BLEduino/bleduino-hardware/BLEduino/PDFs/BLEduino_PCB_copper_2.pdf

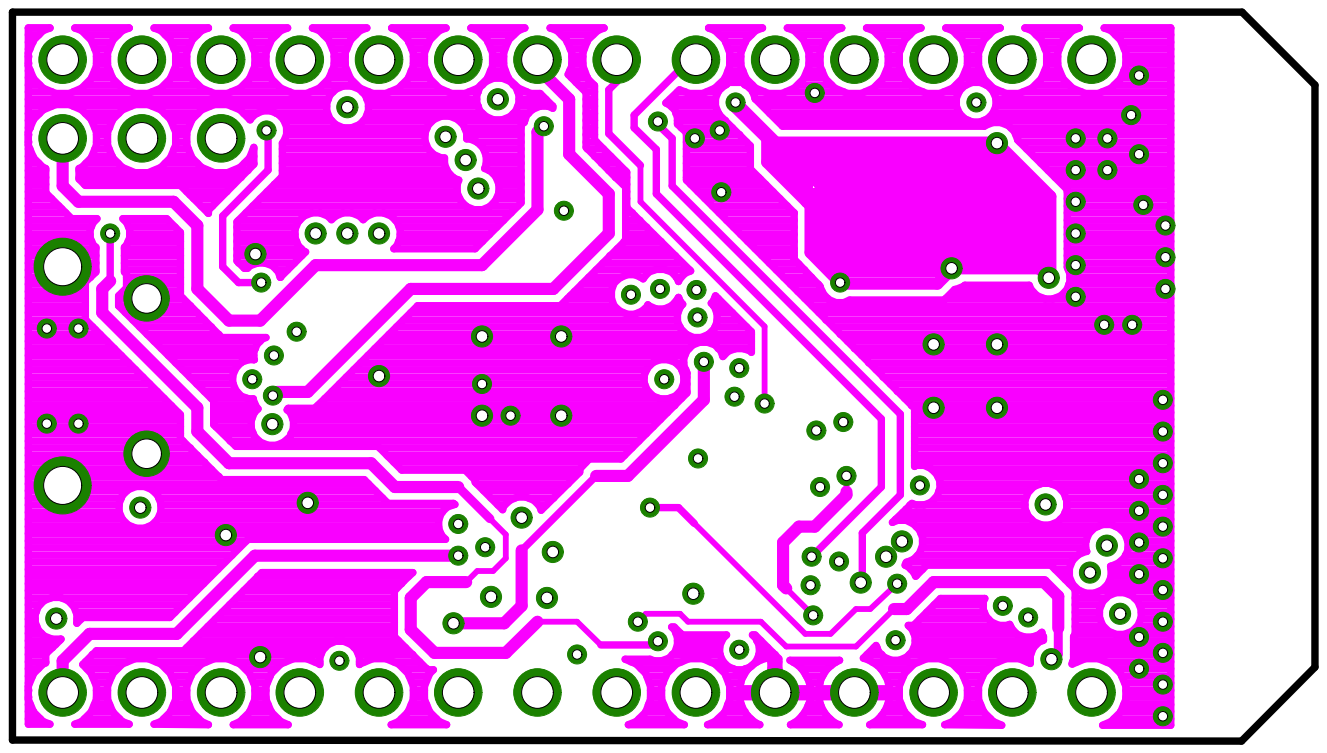
[picture p11: page 1]
