BLEduino/bleduino-hardware/BLEduino/PDFs/BLEduino_PCB_copper_3.pdf

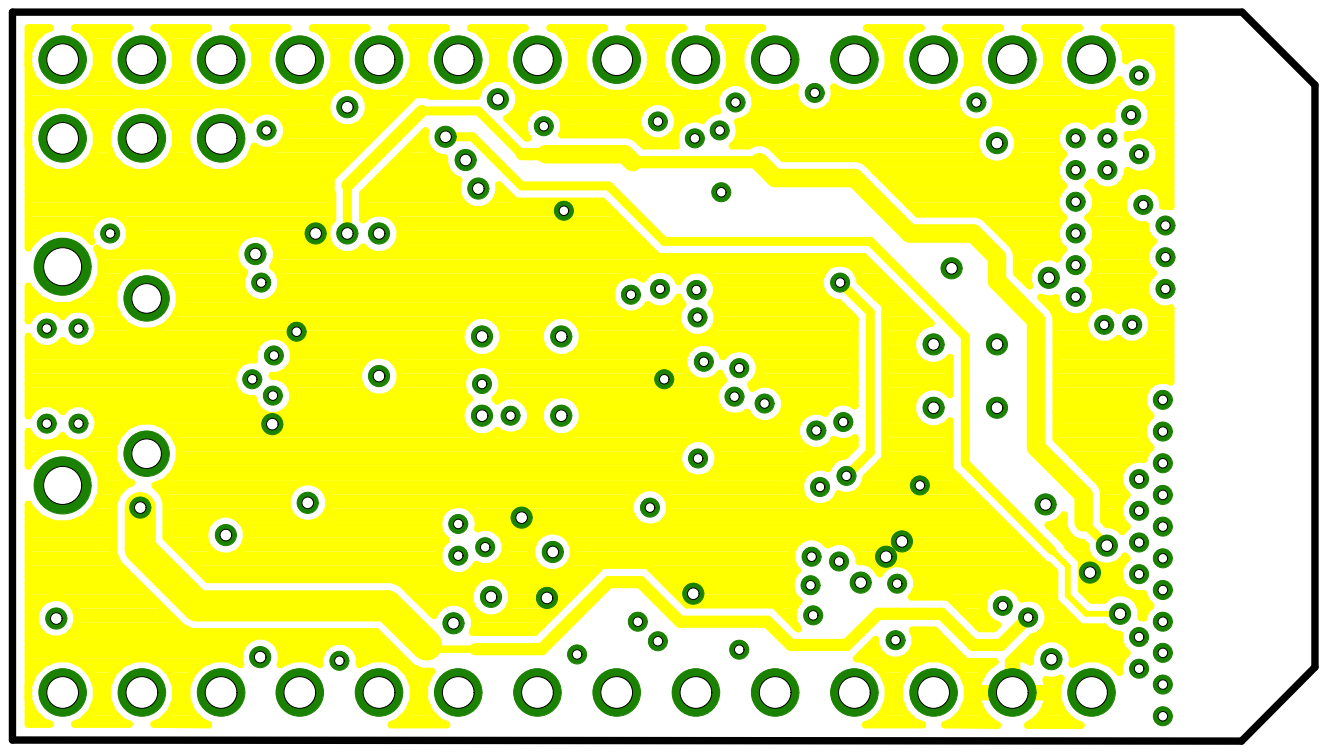
[picture p12: page 1]
