BLEduino/bleduino-hardware/BLEduino/PDFs/BLEduino_PCB_copper_4.pdf

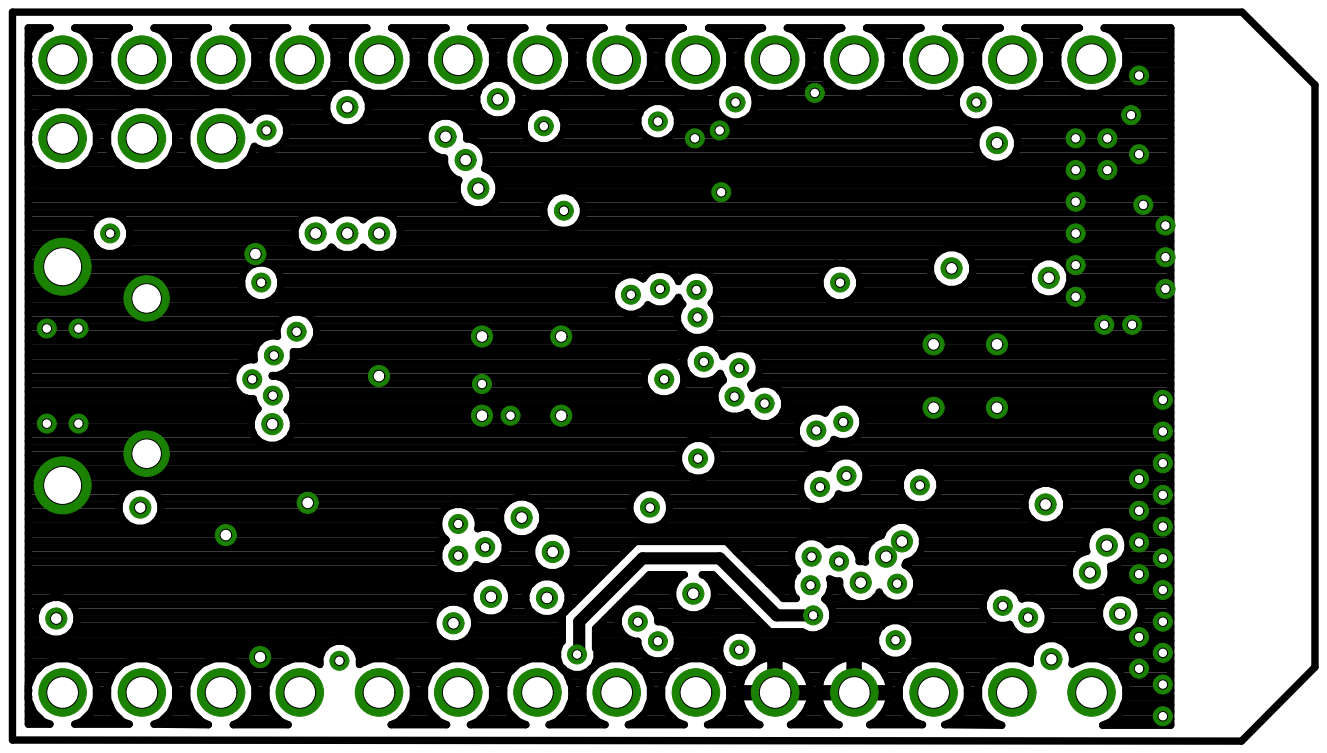
[picture p13: page 1]
