BLEduino/bleduino-hardware/BLEduino/PDFs/BLEduino_PCB_copper_5.pdf

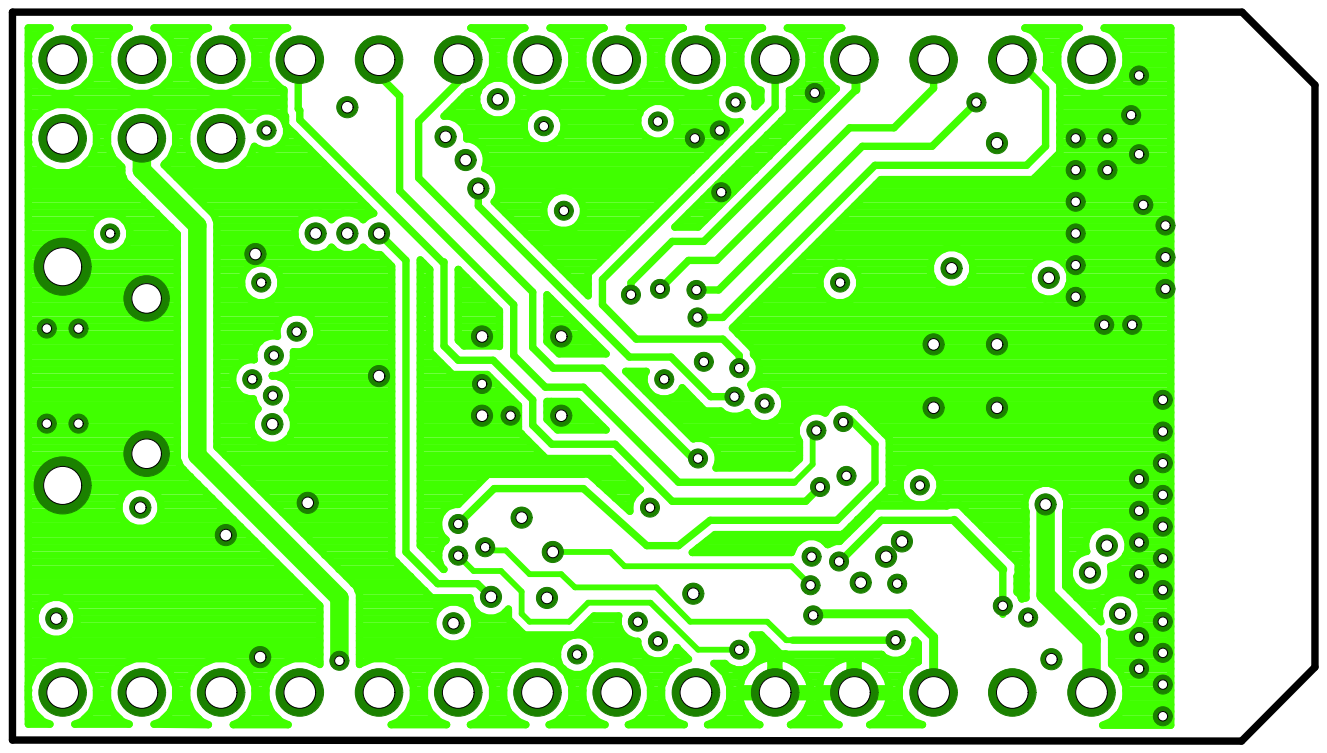
[picture p14: page 1]
