BLEduino/bleduino-hardware/BLEduino/PDFs/BLEduino_PCB_copper_6.pdf

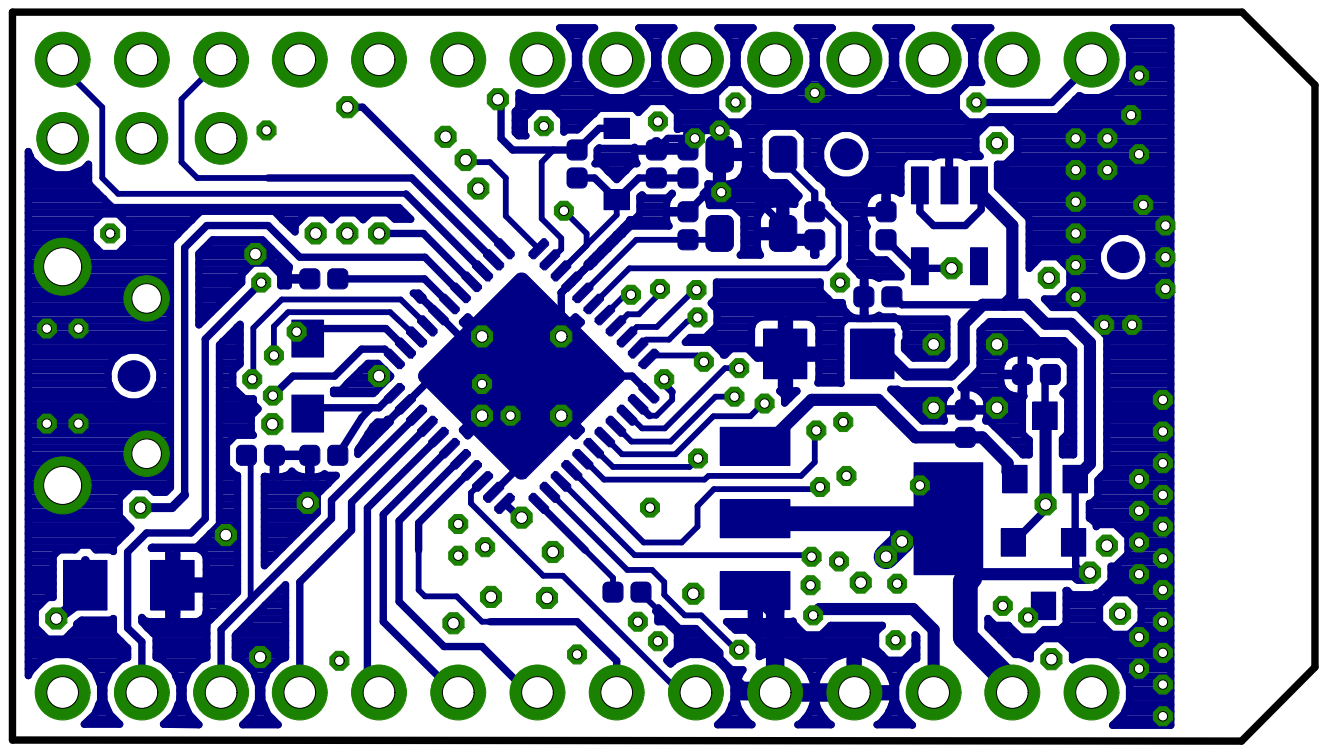
[picture p15: page 1]
